bbow691-png/ECSE_Design_Competition/godot/ecse-design/assets/Spritesheets/Bamboo_bg.png

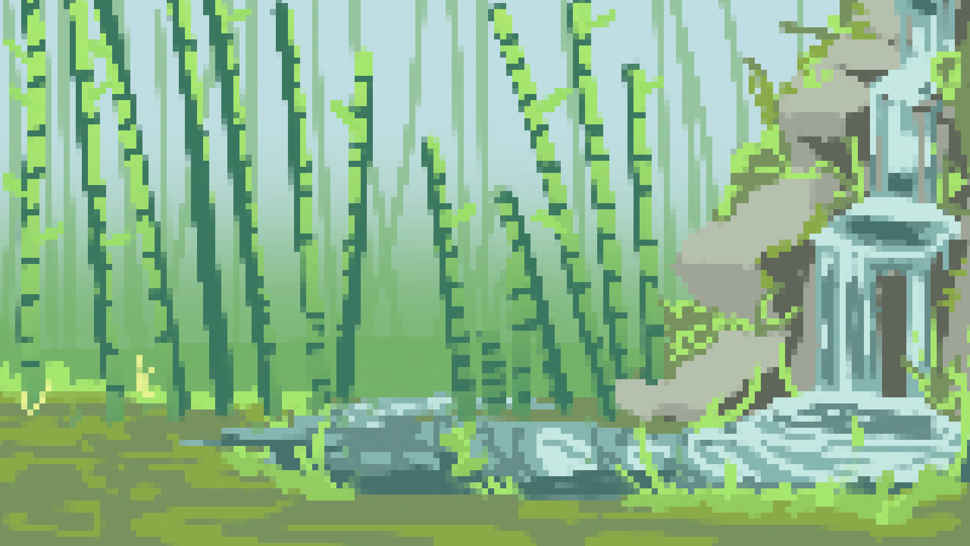
godot/ecse-design/assets/Spritesheets/Bamboo_bg.png
