bbow691-png/ECSE_Design_Competition/beatmaps/mainmenu/selfie.jpg

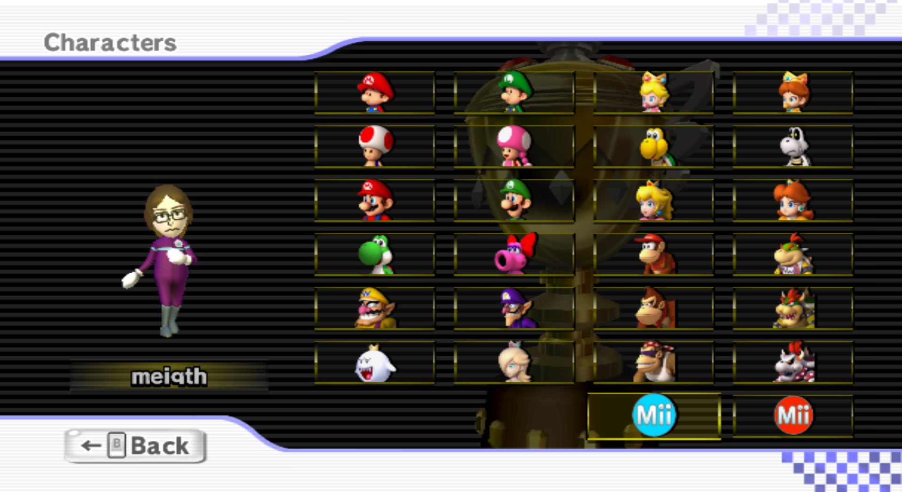
beatmaps/mainmenu/selfie.jpg
