bbow691-png/ECSE_Design_Competition/ECSE Design Hardware Files/Final board/PCM5102A.png

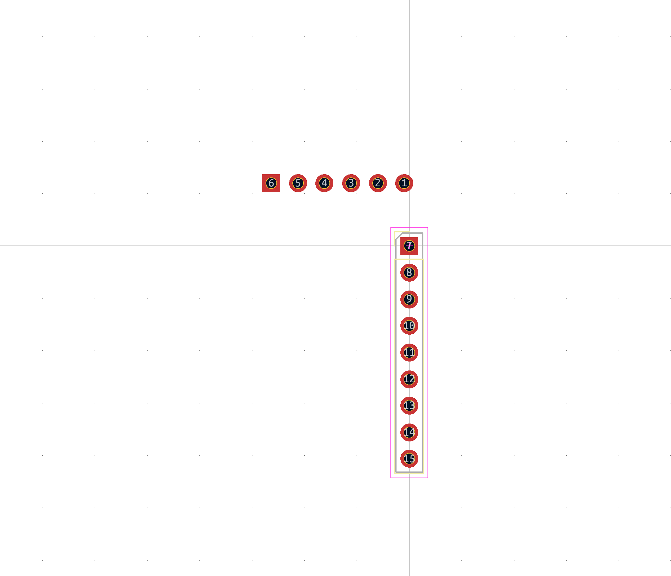
ECSE Design Hardware Files/Final board/PCM5102A.png
