bbow691-png/ECSE_Design_Competition/godot/ecse-design/assets/images/IMG_1008.PNG

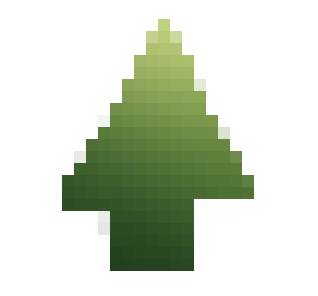
godot/ecse-design/assets/images/IMG_1008.PNG
