bbow691-png/ECSE_Design_Competition/godot/ecse-design/assets/images/snare.png

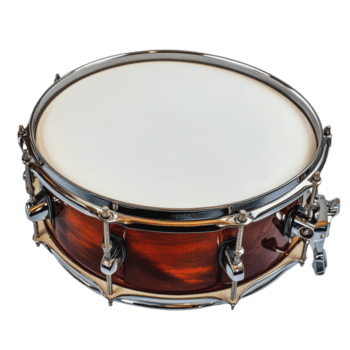
godot/ecse-design/assets/images/snare.png
