bbow691-png/ECSE_Design_Competition/godot/ecse-design/assets/images/The_drums.png

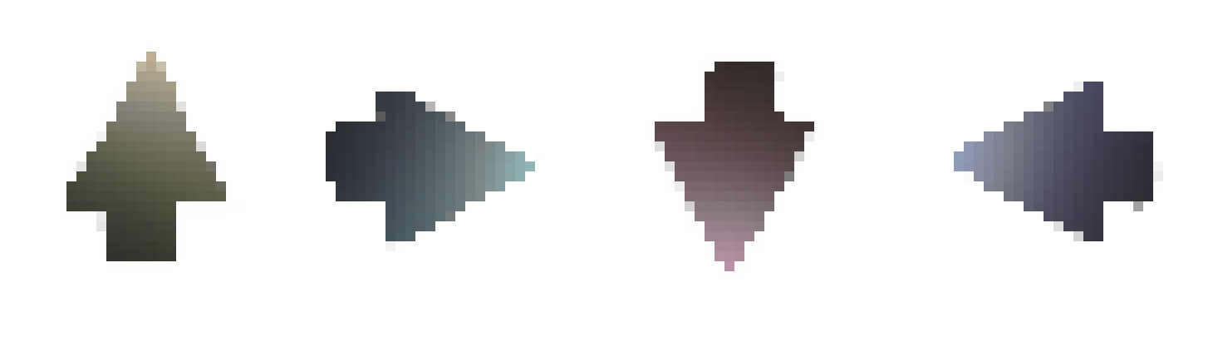
godot/ecse-design/assets/images/The_drums.png
