bbow691-png/ECSE_Design_Competition/godot/ecse-design/assets/Spritesheets/idle_spritesheet.png

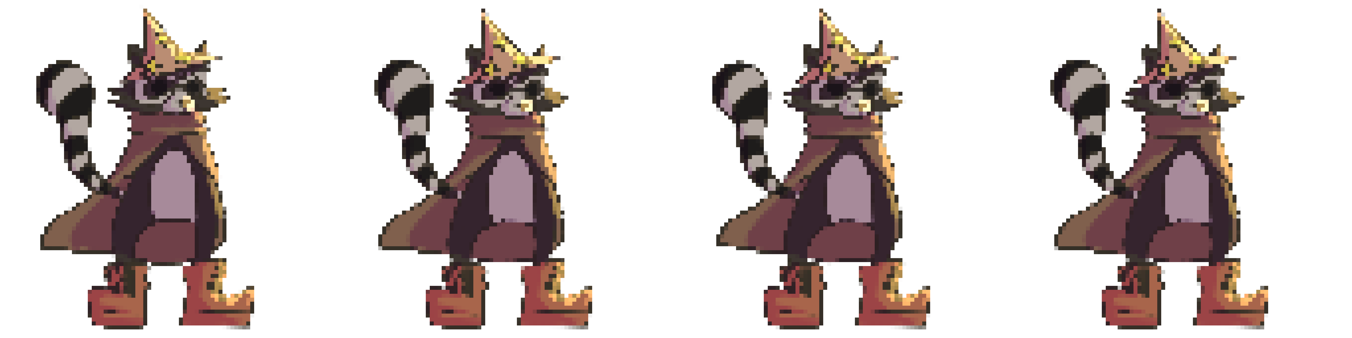
godot/ecse-design/assets/Spritesheets/idle_spritesheet.png
