bbow691-png/ECSE_Design_Competition/godot/ecse-design/assets/Spritesheets/M1_transition_spritesheet.png

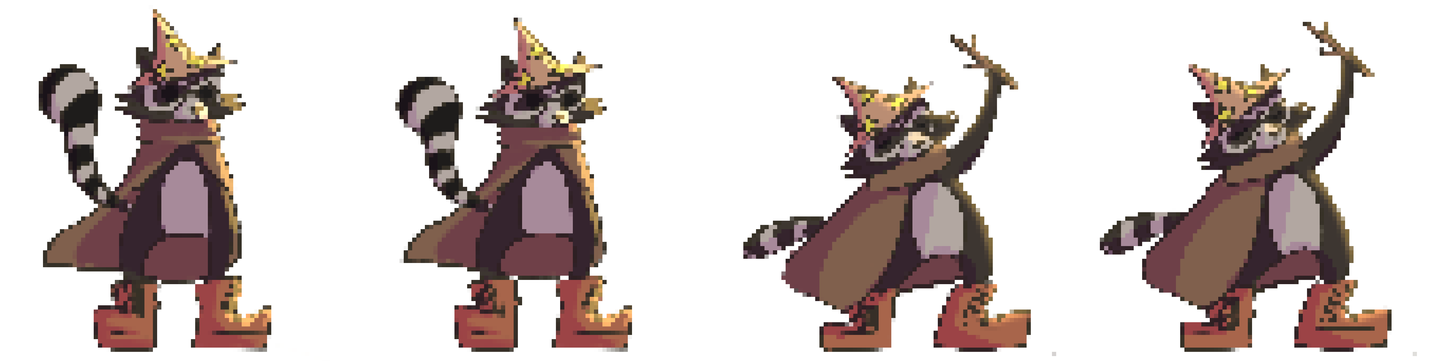
godot/ecse-design/assets/Spritesheets/M1_transition_spritesheet.png
