bbow691-png/ECSE_Design_Competition/godot/ecse-design/assets/Spritesheets/WorldMap.png

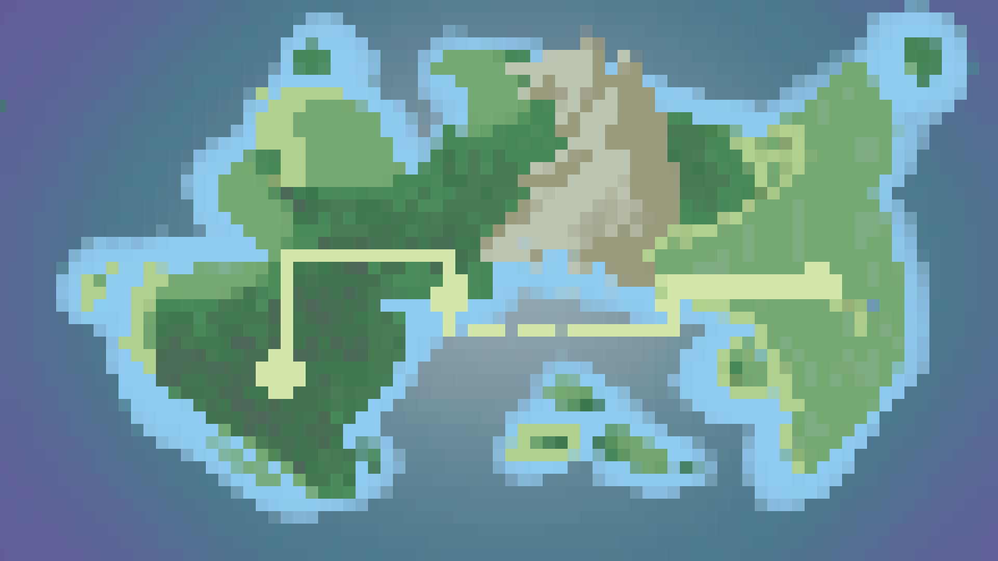
godot/ecse-design/assets/Spritesheets/WorldMap.png
